sdalimon/TeensyWheel/Documentation/PCB_RevEng/Wheel_Schematic.png

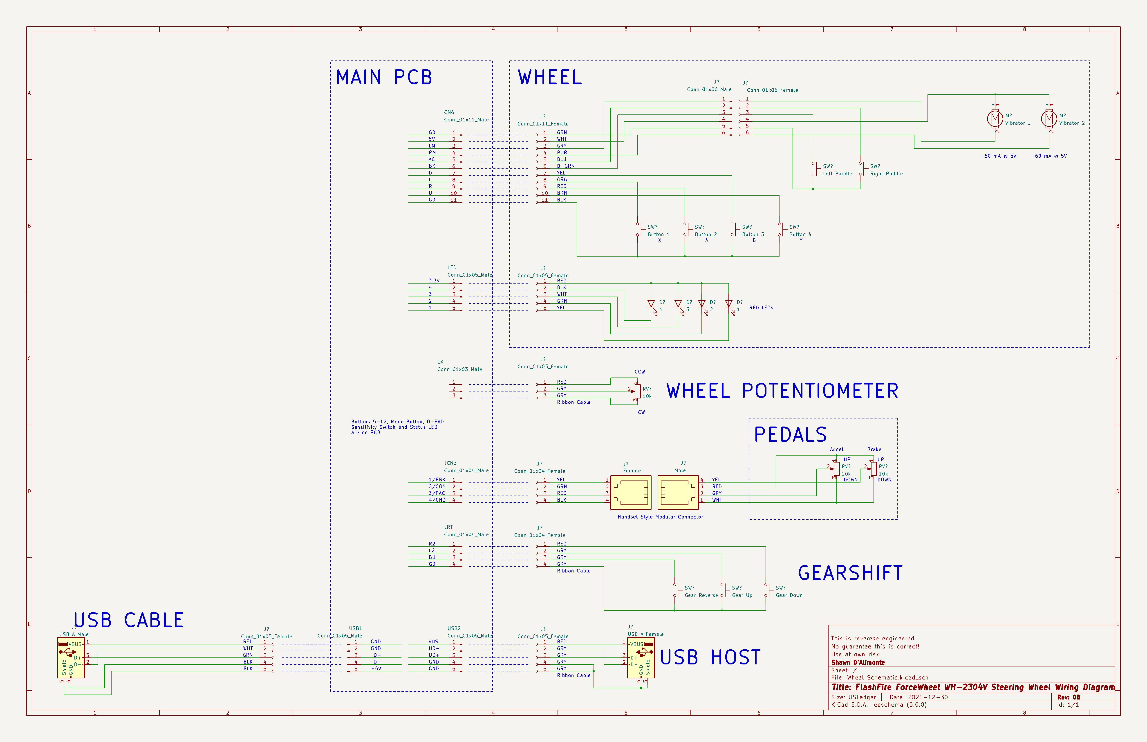
Documentation/PCB_RevEng/Wheel_Schematic.png
